DerekK44/PIC_WaferProbeSystem/hardware/purchased components/MB618-Solidworks.sldprt

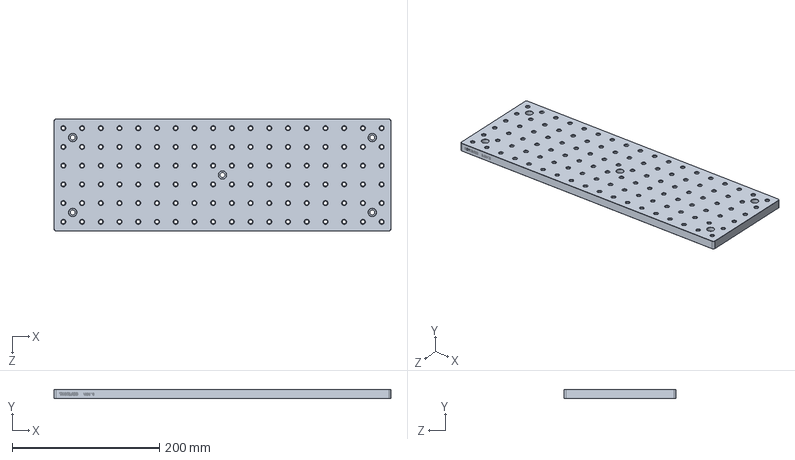
[picture p17: CAD file, 2019-02-19]
hardware/purchased components/MB618-Solidworks.sldprt
457.2 x 12.7 x 152.4 mm
