DerekK44/PIC_WaferProbeSystem/hardware/purchased components/HFV002-Solidworks.sldprt

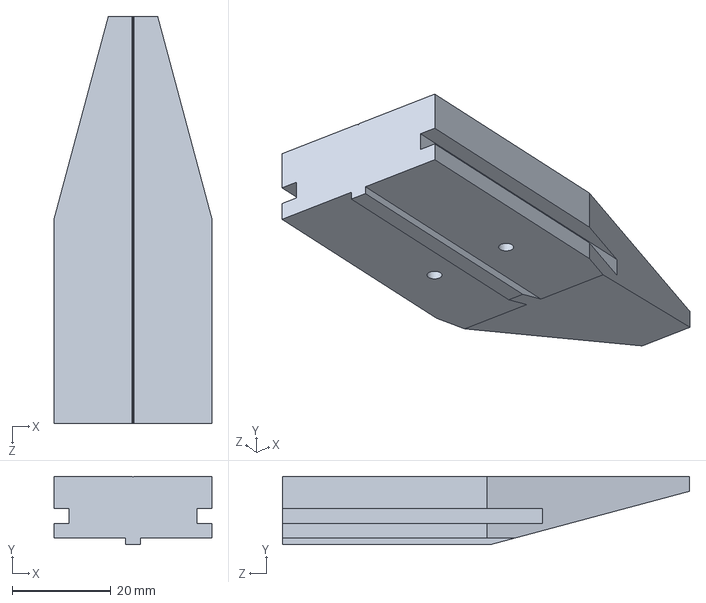
[picture p18: CAD file, 2019-02-19]
hardware/purchased components/HFV002-Solidworks.sldprt
32.0 x 13.8 x 82.5 mm
