DerekK44/PIC_WaferProbeSystem/hardware/purchased components/HR-1.SLDPRT

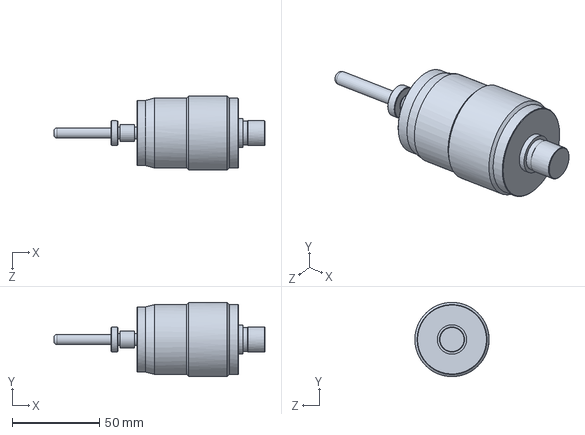
[picture p19: CAD file, 2019-02-19]
hardware/purchased components/HR-1.SLDPRT
120.7 x 42.4 x 42.5 mm
