DerekK44/PIC_WaferProbeSystem/hardware/purchased components/GN2- no base.SLDPRT

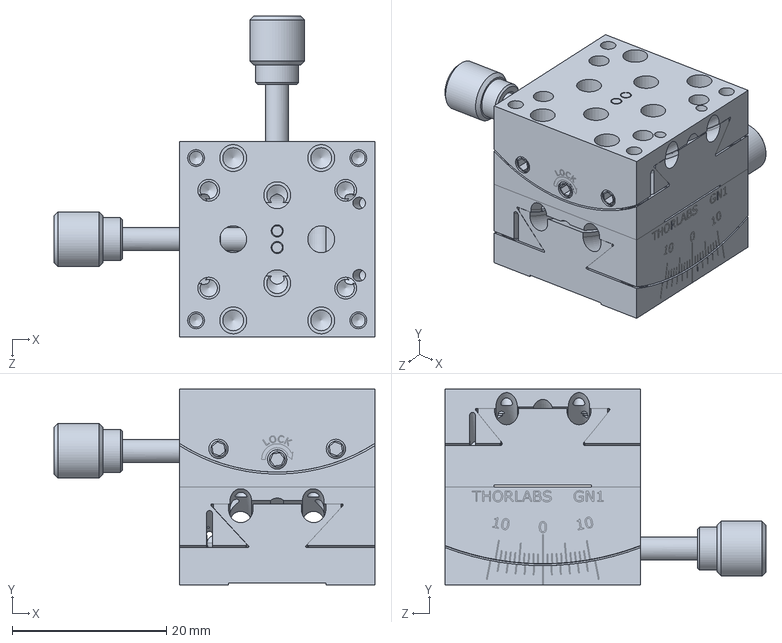
[picture p20: CAD file, 2019-02-19]
hardware/purchased components/GN2- no base.SLDPRT
41.7 x 25.4 x 41.7 mm
