DerekK44/PIC_WaferProbeSystem/hardware/purchased components/M-406.62S.SLDPRT

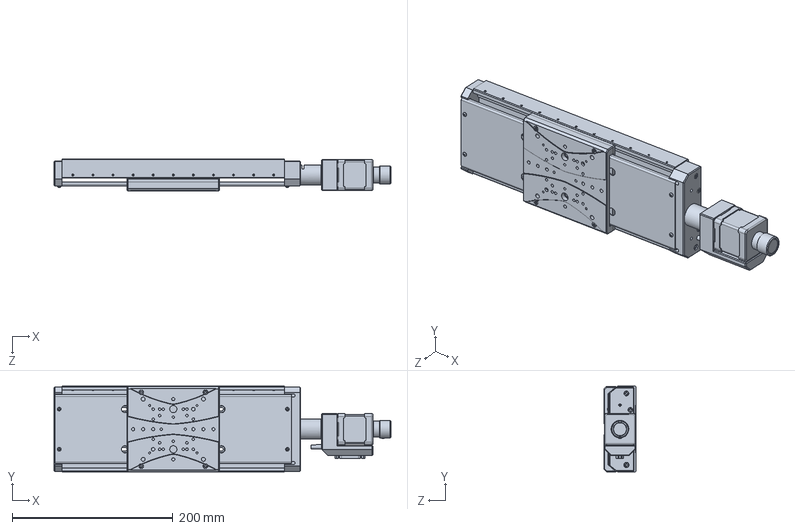
[picture p21: CAD file, 2019-02-19]
hardware/purchased components/M-406.62S.SLDPRT
419.5 x 106.5 x 40.0 mm
